MStefan99/OpenGimbal/3D/Head/Handle spacer.STEP

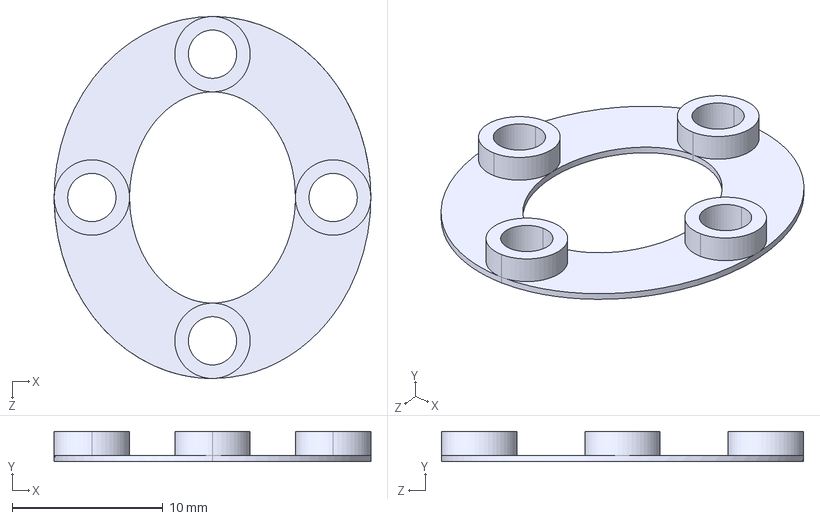
[picture p15: CAD file, 2026-09-18]
3D/Head/Handle spacer.STEP
21.0 x 2.00 x 24.0 mm
