MStefan99/OpenGimbal/3D/Head/Motor cover.STEP

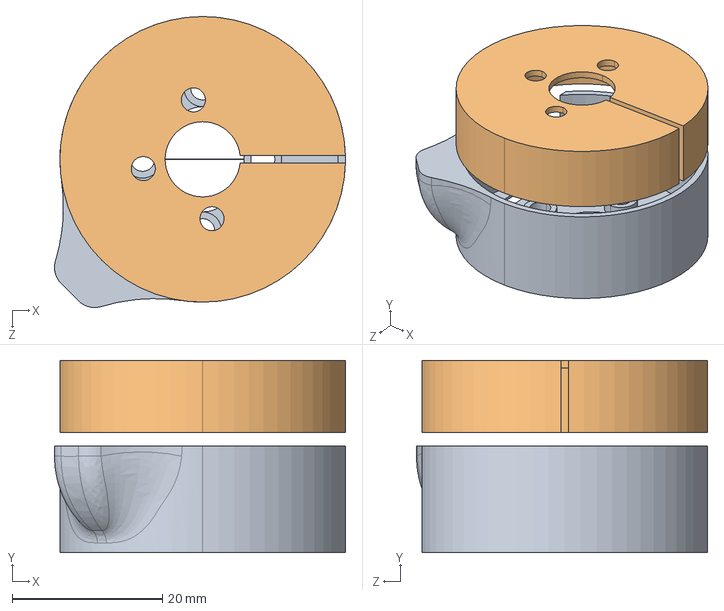
[picture p16: CAD file, 2026-09-18]
3D/Head/Motor cover.STEP
38.7 x 25.6 x 38.7 mm
