MStefan99/OpenGimbal/3D/Head/Upper arm.STEP

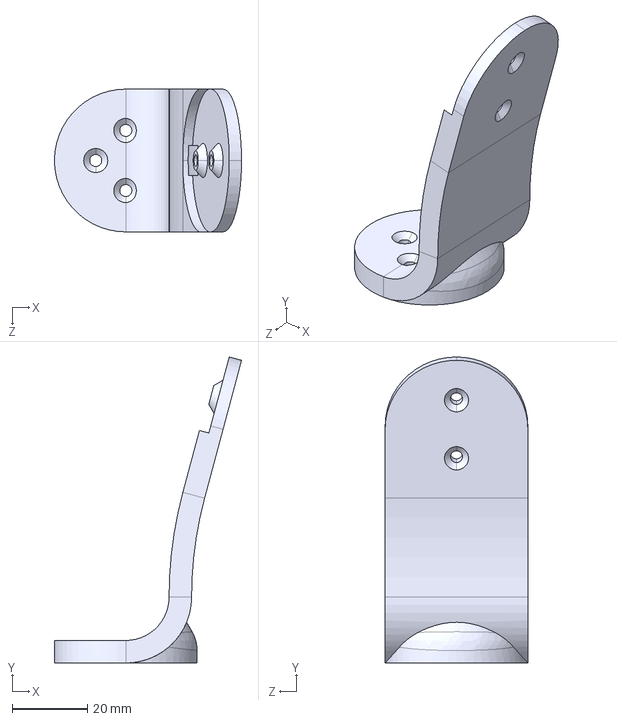
[picture p17: CAD file, 2026-09-18]
3D/Head/Upper arm.STEP
49.8 x 81.5 x 38.0 mm
