MStefan99/OpenGimbal/3D/Head/Motor cover upper.STEP

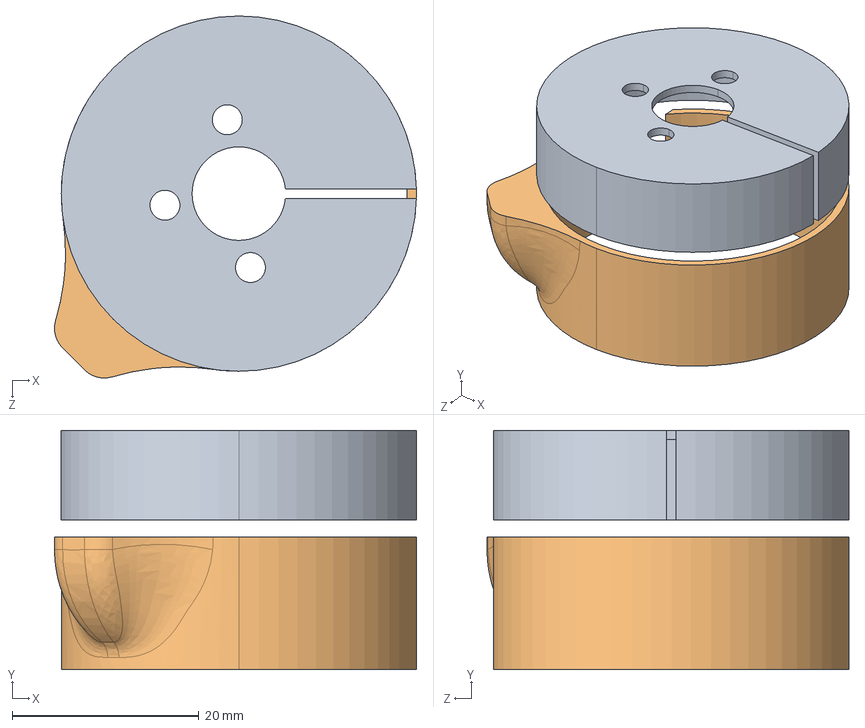
[picture p18: CAD file, 2026-09-18]
3D/Head/Motor cover upper.STEP
38.7 x 25.6 x 38.7 mm
