MStefan99/OpenGimbal/firmware/controller/src/usb.cpp

#include "usb.hpp"

using namespace usb;


static void controlHandler();
static void standardRequestHandler();
static void vendorRequestHandler();
static void enableEndpoints(uint8_t configurationNumber);
static void endpoint1Handler();


#define MIN(a, b) ((a < b) ? (a) : (b))


#define BMREQUESTTYPE_DPTD(bmRequestType)      ((bmRequestType & 0x80) >> 7)
#define BMREQUESTTYPE_TYPE(bmRequestType)      ((bmRequestType & 0x60) >> 5)
#define BMREQUESTTYPE_RECIPIENT(bmRequestType) (bmRequestType & 0x1f)

#define WVALUE_TYPE(wValue) ((wValue & 0xff00) >> 8)
#define WVALUE_IDX(wValue)  (wValue & 0xff)
#define WVALUE_ADD(wValue)  (wValue & 0x7f)

typedef struct __attribute__((packed)) {
	uint8_t  bmRequestType;
	uint8_t  bRequest;
	uint16_t wValue;
	uint16_t wIndex;
	uint16_t wLength;
} usb_device_endpoint0_request;

usb_descriptor_device_registers_t usb::EPDESCTBL[2];

static usb_device_endpoint0_request EP0REQ;
static usb_device_endpoint1_request EP1REQ;

static uint8_t* defaultData {nullptr};
static uint8_t  defaultLen {0};

static uint8_t outBuffer[128];

static usb::suspend_callback_type suspendCallback {nullptr};
static usb::callback_type         callback {nullptr};


extern "C" {
	void USB_Handler() {
		if (USB_REGS->DEVICE.USB_INTFLAG & USB_DEVICE_INTFLAG_SUSPEND_Msk) {  // Process USB reset
			USB_REGS->DEVICE.USB_INTFLAG = USB_DEVICE_INTFLAG_SUSPEND(1);       // Clear pending interrupt
			if (suspendCallback) {
				suspendCallback(true);
			}
		}

		if (USB_REGS->DEVICE.USB_INTFLAG & USB_DEVICE_INTFLAG_WAKEUP_Msk) {  // Process USB wakeup
			USB_REGS->DEVICE.USB_INTFLAG = USB_DEVICE_INTFLAG_WAKEUP(1);       // Clear pending interrupt
			if (suspendCallback) {
				suspendCallback(false);
			}
		}

		if (USB_REGS->DEVICE.USB_INTFLAG & USB_DEVICE_INTFLAG_EORST_Msk) {  // Process USB reset
			USB_REGS->DEVICE.USB_INTFLAG = USB_DEVICE_INTFLAG_EORST(1);       // Clear pending interrupt
			USB_REGS->DEVICE.DEVICE_ENDPOINT[0].USB_EPINTENSET =
			    USB_DEVICE_EPINTENSET_RXSTP(1)      // Enable SETUP endpoint interrupt
			    | USB_DEVICE_EPINTENSET_TRCPT0(1)   // Enable OUT endpoint interrupt
			    | USB_DEVICE_EPINTENSET_TRCPT1(1);  // Enable IN endpoint interrupt
			EPDESCTBL[0].DEVICE_DESC_BANK[0].USB_ADDR = (uint32_t)&EP0REQ;
		}

		if (USB_REGS->DEVICE.DEVICE_ENDPOINT[0].USB_EPINTFLAG
		    & (USB_DEVICE_EPINTFLAG_RXSTP_Msk | USB_DEVICE_EPINTFLAG_TRCPT1_Msk | USB_DEVICE_EPINTFLAG_TRCPT0_Msk)) {
			controlHandler();
		} else if (USB_REGS->DEVICE.DEVICE_ENDPOINT[1].USB_EPINTFLAG
		           & (USB_DEVICE_EPINTFLAG_TRCPT1_Msk | USB_DEVICE_EPINTFLAG_TRCPT0_Msk)) {
			endpoint1Handler();
			USB_REGS->DEVICE.DEVICE_ENDPOINT[1].USB_EPSTATUSCLR = USB_DEVICE_EPSTATUS_BK0RDY(1);
			USB_REGS->DEVICE.DEVICE_ENDPOINT[1].USB_EPINTFLAG =
			    USB_DEVICE_EPINTFLAG_Msk;  // Clear all pending endpoint interrupts
		}
	}
}

static void controlHandler() {
	if (USB_REGS->DEVICE.DEVICE_ENDPOINT[0].USB_EPINTFLAG & USB_DEVICE_EPINTFLAG_RXSTP_Msk) {  // Process SETUP transfers
		USB_REGS->DEVICE.DEVICE_ENDPOINT[0].USB_EPINTFLAG = USB_DEVICE_EPINTFLAG_RXSTP(1);       // Clear pending interrupt
		switch (static_cast<REQ_TYPE>(BMREQUESTTYPE_TYPE(EP0REQ.bmRequestType))) {
			case REQ_TYPE::STANDARD:
				standardRequestHandler();
				break;
			case REQ_TYPE::CLASS:
				// TODO: Handle
				break;
			case REQ_TYPE::VENDOR:
				vendorRequestHandler();
				break;
		}
		USB_REGS->DEVICE.DEVICE_ENDPOINT[0].USB_EPSTATUSSET = USB_DEVICE_EPSTATUS_BK1RDY(1);
		USB_REGS->DEVICE.DEVICE_ENDPOINT[0].USB_EPSTATUSCLR = USB_DEVICE_EPSTATUS_BK0RDY(1);
	}

	if (USB_REGS->DEVICE.DEVICE_ENDPOINT[0].USB_EPINTFLAG & USB_DEVICE_EPINTFLAG_TRCPT0_Msk) {  // Process OUT transfers
		USB_REGS->DEVICE.DEVICE_ENDPOINT[0].USB_EPINTFLAG = USB_DEVICE_EPINTFLAG_TRCPT0(1);       // Clear pending interrupt
		USB_REGS->DEVICE.DEVICE_ENDPOINT[0].USB_EPSTATUSSET = USB_DEVICE_EPSTATUS_BK1RDY(1);
	}

	if (USB_REGS->DEVICE.DEVICE_ENDPOINT[0].USB_EPINTFLAG & USB_DEVICE_EPINTFLAG_TRCPT1_Msk) {  // Process IN transfers
		USB_REGS->DEVICE.DEVICE_ENDPOINT[0].USB_EPINTFLAG = USB_DEVICE_EPINTFLAG_TRCPT1(1);       // Clear pending interrupt
		if (USB_REGS->DEVICE.USB_DADD && !(USB_REGS->DEVICE.USB_DADD & USB_DEVICE_DADD_ADDEN_Msk)) {
			USB_REGS->DEVICE.USB_DADD |= USB_DEVICE_DADD_ADDEN(1);
		}
	}
}

static void standardRequestHandler() {
	switch (static_cast<DEVICE_REQ>(EP0REQ.bRequest)) {
		case DEVICE_REQ::GET_DESCRIPTOR:
			switch (static_cast<DESCRIPTOR_TYPE>(WVALUE_TYPE(EP0REQ.wValue))) {
				case DESCRIPTOR_TYPE::DEVICE:
					EPDESCTBL[0].DEVICE_DESC_BANK[1].USB_ADDR = reinterpret_cast<uint32_t>(&DESCRIPTOR_DEVICE);
					EPDESCTBL[0].DEVICE_DESC_BANK[1].USB_PCKSIZE =
					    USB_DEVICE_PCKSIZE_BYTE_COUNT(MIN(DESCRIPTOR_DEVICE.bLength, EP0REQ.wLength))
					    | USB_DEVICE_PCKSIZE_SIZE(0x3) | USB_DEVICE_PCKSIZE_AUTO_ZLP(1);
					break;
				case DESCRIPTOR_TYPE::BOS:
					EPDESCTBL[0].DEVICE_DESC_BANK[1].USB_ADDR = reinterpret_cast<uint32_t>(&DESCRIPTOR_BOS);
					EPDESCTBL[0].DEVICE_DESC_BANK[1].USB_PCKSIZE =
					    USB_DEVICE_PCKSIZE_BYTE_COUNT(MIN(DESCRIPTOR_BOS.wTotalLength, EP0REQ.wLength))
					    | USB_DEVICE_PCKSIZE_SIZE(0x3) | USB_DEVICE_PCKSIZE_AUTO_ZLP(1);
					break;
				case DESCRIPTOR_TYPE::CONFIGURATION:
					EPDESCTBL[0].DEVICE_DESC_BANK[1].USB_ADDR =
					    reinterpret_cast<uint32_t>(&(DESCRIPTOR_CONFIGURATION[WVALUE_IDX(EP0REQ.wValue)]));
					EPDESCTBL[0].DEVICE_DESC_BANK[1].USB_PCKSIZE =
					    USB_DEVICE_PCKSIZE_BYTE_COUNT(
					        MIN(DESCRIPTOR_CONFIGURATION[WVALUE_IDX(EP0REQ.wValue)].wTotalLength, EP0REQ.wLength)
					    )
					    | USB_DEVICE_PCKSIZE_SIZE(0x3) | USB_DEVICE_PCKSIZE_AUTO_ZLP(1);
					break;
				case DESCRIPTOR_TYPE::STRING: {
					uint8_t idx = WVALUE_IDX(EP0REQ.wValue);
					if (idx <= sizeof(usb::DESCRIPTOR_STRING) / sizeof(usb::DESCRIPTOR_STRING[0])) {
						EPDESCTBL[0].DEVICE_DESC_BANK[1].USB_ADDR = reinterpret_cast<uint32_t>(&(DESCRIPTOR_STRING[idx]));
						EPDESCTBL[0].DEVICE_DESC_BANK[1].USB_PCKSIZE =
						    USB_DEVICE_PCKSIZE_BYTE_COUNT(MIN(DESCRIPTOR_STRING[idx].bLength, EP0REQ.wLength))
						    | USB_DEVICE_PCKSIZE_SIZE(0x3) | USB_DEVICE_PCKSIZE_AUTO_ZLP(1);
					} else {
						USB_REGS->DEVICE.DEVICE_ENDPOINT[0].USB_EPSTATUSSET = USB_DEVICE_EPSTATUSCLR_STALLRQ1(1);
					}
					break;
				}
				case DESCRIPTOR_TYPE::DEVICE_QUALIFIER:
					USB_REGS->DEVICE.DEVICE_ENDPOINT[0].USB_EPSTATUSSET = USB_DEVICE_EPSTATUSCLR_STALLRQ1(1);
					break;
				default:
					// TODO: Handle
					break;
			}
			USB_REGS->DEVICE.DEVICE_ENDPOINT[0].USB_EPSTATUSSET = USB_DEVICE_EPSTATUS_BK1RDY(1);
			break;
		case DEVICE_REQ::SET_ADDRESS:
			USB_REGS->DEVICE.USB_DADD = WVALUE_ADD(EP0REQ.wValue);
			EPDESCTBL[0].DEVICE_DESC_BANK[1].USB_PCKSIZE = USB_DEVICE_PCKSIZE_AUTO_ZLP(1);
			break;
		case DEVICE_REQ::SET_CONFIGURATION:
			EPDESCTBL[0].DEVICE_DESC_BANK[1].USB_PCKSIZE = USB_DEVICE_PCKSIZE_AUTO_ZLP(1);
			enableEndpoints(EP0REQ.wValue);
			break;
		default:
			// TODO: Handle
			break;
	}
}

static void vendorRequestHandler() {
	if (EP0REQ.bRequest == 0x01) {
		EPDESCTBL[0].DEVICE_DESC_BANK[1].USB_ADDR = reinterpret_cast<uint32_t>(&DESCRIPTOR_MS_OS_20);
		EPDESCTBL[0].DEVICE_DESC_BANK[1].USB_PCKSIZE =
		    USB_DEVICE_PCKSIZE_BYTE_COUNT(MIN(DESCRIPTOR_MS_OS_20.wTotalLength, EP0REQ.wLength))
		    | USB_DEVICE_PCKSIZE_SIZE(0x3) | USB_DEVICE_PCKSIZE_AUTO_ZLP(1);
	}
}

void endpoint1Handler() {
	if (USB_REGS->DEVICE.DEVICE_ENDPOINT[1].USB_EPINTFLAG & USB_DEVICE_EPINTFLAG_TRCPT0_Msk) {  // OUT transfer
		if (callback) {
			callback(EP1REQ, EPDESCTBL[1].DEVICE_DESC_BANK[0].USB_PCKSIZE & USB_DEVICE_PCKSIZE_BYTE_COUNT_Msk);
		}

		EPDESCTBL[1].DEVICE_DESC_BANK[0].USB_PCKSIZE =
		    USB_DEVICE_PCKSIZE_MULTI_PACKET_SIZE(sizeof(EP1REQ)) | USB_DEVICE_PCKSIZE_SIZE(0x3);
		return;
	} else if (defaultLen) {
		write(defaultData, defaultLen);
	}
}

static void enableEndpoints(uint8_t configurationNumber) {
	USB_REGS->DEVICE.DEVICE_ENDPOINT[1].USB_EPCFG =
	    USB_DEVICE_EPCFG_EPTYPE0(0x4)     // Configure endpoint 1 bank 0 as interrupt out
	    | USB_DEVICE_EPCFG_EPTYPE1(0x4);  // Configure endpoint 1 bank 1 as interrupt in
	EPDESCTBL[1].DEVICE_DESC_BANK[0].USB_ADDR = reinterpret_cast<uint32_t>(&EP1REQ);
	EPDESCTBL[1].DEVICE_DESC_BANK[0].USB_PCKSIZE =
	    USB_DEVICE_PCKSIZE_MULTI_PACKET_SIZE(sizeof(EP1REQ)) | USB_DEVICE_PCKSIZE_SIZE(0x3);
	USB_REGS->DEVICE.DEVICE_ENDPOINT[1].USB_EPINTENSET = USB_DEVICE_EPINTENSET_TRCPT0(1)  // Enable OUT endpoint interrupt
	                                                   | USB_DEVICE_EPINTENSET_TRCPT1(1);  // Enable IN endpoint interrupt
}

void usb::init() {
	auto id = (reinterpret_cast<uint32_t*>(0x0080A00C));

	usb::DESCRIPTOR_STRING[3].bLength = 66;
	for (uint8_t i {0}; i < 4; ++i) {
		uint32_t word {id[i]};
		for (int8_t j {7}; j >= 0; --j) {
			uint8_t c = word & 0xf;
			usb::DESCRIPTOR_STRING[3].bString[8 * i + j] = c + (c < 0xa ? 0x0030 : 0x0037);
			word = word >> 4u;
		}
	}

	GCLK_REGS->GCLK_PCHCTRL[USB_GCLK_ID] = GCLK_PCHCTRL_CHEN(1)     // Enable USB clock
	                                     | GCLK_PCHCTRL_GEN_GCLK1;  // Set GCLK1 as a clock source

	NVIC_EnableIRQ(USB_IRQn);

	PORT_REGS->GROUP[0].PORT_PINCFG[24] = PORT_PINCFG_PMUXEN(1);  // Enable mux on pin 24
	PORT_REGS->GROUP[0].PORT_PINCFG[25] = PORT_PINCFG_PMUXEN(1);  // Enable mux on pin 25
	PORT_REGS->GROUP[0].PORT_PMUX[12] = PORT_PMUX_PMUXE_G         // Mux pin 24 to USB
	                                  | PORT_PMUX_PMUXO_G;        // Mux pin 25 to USB

	USB_REGS->DEVICE.USB_PADCAL =
	    USB_PADCAL_TRANSN(
	        (OTP5_FUSES_REGS->FUSES_OTP5_WORD_0 & FUSES_OTP5_WORD_0_USB_TRANSN_Msk) >> FUSES_OTP5_WORD_0_USB_TRANSN_Pos
	    )
	    | USB_PADCAL_TRANSP(
	        (OTP5_FUSES_REGS->FUSES_OTP5_WORD_0 & FUSES_OTP5_WORD_0_USB_TRANSP_Msk) >> FUSES_OTP5_WORD_0_USB_TRANSP_Pos
	    )
	    | USB_PADCAL_TRIM(
	        (OTP5_FUSES_REGS->FUSES_OTP5_WORD_0 & FUSES_OTP5_WORD_0_USB_TRIM_Msk) >> FUSES_OTP5_WORD_0_USB_TRIM_Pos
	    );                                                                          // USB pad calibration
	USB_REGS->DEVICE.USB_CTRLA = USB_CTRLA_ENABLE(1)                                // Enable USB
	                           | USB_CTRLA_MODE_DEVICE;                             // Enable in device mode
	USB_REGS->DEVICE.DEVICE_ENDPOINT[0].USB_EPCFG = USB_DEVICE_EPCFG_EPTYPE0(0x1)   // Configure endpoint 0 as setup out
	                                              | USB_DEVICE_EPCFG_EPTYPE1(0x1);  // Configure endpoint 0 as setup in
	USB_REGS->DEVICE.USB_DESCADD = reinterpret_cast<uint32_t>(&EPDESCTBL);          // Setting endpoint descriptor address
	USB_REGS->DEVICE.USB_CTRLB = USB_DEVICE_CTRLB_DETACH(0);                        // Attach to host
	USB_REGS->DEVICE.USB_INTENSET = USB_DEVICE_INTENSET_EORST(1)                    // Enable end-of-reset interrupt
	                              | USB_DEVICE_INTENSET_WAKEUP(1)                   // Enable wakeup interrupt
	                              | USB_DEVICE_INTENSET_SUSPEND(1);                 // Enable suspend interrupt
}

bool usb::isActive() {
	return USB_REGS->DEVICE.USB_FSMSTATUS != USB_FSMSTATUS_FSMSTATE_OFF
	    && USB_REGS->DEVICE.USB_FSMSTATUS != USB_FSMSTATUS_FSMSTATE_SUSPEND;
}

void usb::writeDefault(uint8_t* data, uint8_t len) {
	defaultData = data;
	defaultLen = len;

	if (!(USB_REGS->DEVICE.DEVICE_ENDPOINT[1].USB_EPSTATUS & USB_DEVICE_EPSTATUS_BK1RDY(0))) {
		write(data, len);
	}
}

void usb::write(const uint8_t* data, uint8_t len) {
	util::copy(outBuffer, data, len);
	EPDESCTBL[1].DEVICE_DESC_BANK[1].USB_ADDR = reinterpret_cast<uint32_t>(outBuffer);
	EPDESCTBL[1].DEVICE_DESC_BANK[1].USB_PCKSIZE =
	    USB_DEVICE_PCKSIZE_BYTE_COUNT(len) | USB_DEVICE_PCKSIZE_SIZE(0x3) | USB_DEVICE_PCKSIZE_AUTO_ZLP(1);
	USB_REGS->DEVICE.DEVICE_ENDPOINT[1].USB_EPSTATUSSET = USB_DEVICE_EPSTATUS_BK1RDY(1);
}

void usb::setSuspendCallback(suspend_callback_type cb) {
	suspendCallback = cb;
}

void usb::setCallback(callback_type cb) {
	callback = cb;
}
