MStefan99/OpenGimbal/firmware/driver/main.hpp

/*
 * File:   main.hpp
 * Author: Mikhail
 *
 * Created on November 8, 2023, 5:24 PM
 */

#ifndef MAIN_HPP
#define MAIN_HPP

#include "device.h"
// #include <xc.h>  // TODO: explore, possibly delete Harmony files

// #include <cstdio>
// #include <cinttypes>

#include "AS5600.hpp"
#include "bldc.hpp"
#include "eic.hpp"
#include "i2c.hpp"
#include "Kalman.hpp"
#include "LowPassFilter.hpp"
#include "Matrix.hpp"
#include "MovementController.hpp"
#include "nvm.hpp"
#include "PID.hpp"
#include "Response.hpp"
#include "uart.hpp"
#include "util.hpp"


enum class Mode : uint8_t {
	Sleep = 0x0,
	Calibrate = 0x1,
	Drive = 0x2,
	Haptic = 0x3,
	Idle = 0x04
};

#endif /* MAIN_HPP */
