MStefan99/OpenGimbal/firmware/controller/src/adc.cpp

#include "adc.hpp"

struct queueEntry {
	adc::Callback cb {nullptr};
	uint16_t      input {};
};

static RingBuffer<queueEntry, uint8_t, 4> measureQueue {};


extern "C" {
	void ADC_Handler() {
		if (measureQueue.size()) {
			auto cb {measureQueue.front().cb};

			if (cb) {
				cb(ADC_REGS->ADC_RESULT);
			}
			measureQueue.pop_front();

			if (measureQueue.size()) {
				ADC_REGS->ADC_INPUTCTRL = ADC_INPUTCTRL_MUXNEG_GND     // Set GND as negative input
				                        | measureQueue.front().input;  // Set temperature sensor as positive input

				ADC_REGS->ADC_SWTRIG = ADC_SWTRIG_START(1);
			}
		}

		ADC_REGS->ADC_INTFLAG = ADC_INTFLAG_Msk;
	}
}

void adc::init() {
	// Clock setup
	GCLK_REGS->GCLK_PCHCTRL[ADC_GCLK_ID] = GCLK_PCHCTRL_CHEN(1)     // Enable ADC clock
	                                     | GCLK_PCHCTRL_GEN_GCLK2;  // Set GCLK2 as a clock source

	// Voltage reference setup
	SUPC_REGS->SUPC_VREF = SUPC_VREF_TSEN(1)      // Enable temperature sensor
	                     | SUPC_VREF_ONDEMAND(1)  // Only enable if requested
	                     | SUPC_VREF_SEL_1V0;     // Set 1.0V as a reference

	// Pin setup
	PORT_REGS->GROUP[0].PORT_WRCONFIG = PORT_WRCONFIG_PINMASK(0x1 << 2u | 0x1 << 3u | 0x1 << 6u)  // Select pins
	                                  | PORT_WRCONFIG_PMUXEN(1)                                   // Enable multiplexing
	                                  | PORT_WRCONFIG_PMUX(MUX_PA02B_ADC_AIN0)                    // Multiplex to ADC
	                                  | PORT_WRCONFIG_WRPMUX(1)     // Write pin multiplex settings
	                                  | PORT_WRCONFIG_WRPINCFG(1);  // Write pin config settings

	// ADC setup
	ADC_REGS->ADC_CTRLB = ADC_CTRLB_PRESCALER_DIV32;  // Set prescaler
	ADC_REGS->ADC_CALIB = ADC_CALIB_BIASREFBUF(
	                          (OTP5_FUSES_REGS->FUSES_OTP5_WORD_0 & FUSES_OTP5_WORD_0_ADC_BIASREFBUF_Msk)
	                          >> FUSES_OTP5_WORD_0_ADC_BIASREFBUF_Pos
	                      )
	                    | ADC_CALIB_BIASCOMP(
	                          (OTP5_FUSES_REGS->FUSES_OTP5_WORD_0 & FUSES_OTP5_WORD_0_ADC_BIASCOMP_Msk)
	                          >> FUSES_OTP5_WORD_0_ADC_BIASCOMP_Pos
	                    );
	ADC_REGS->ADC_SAMPCTRL = ADC_SAMPCTRL_OFFCOMP(1);                         // Enable offset compensation
	ADC_REGS->ADC_AVGCTRL = ADC_AVGCTRL_SAMPLENUM_8 | ADC_AVGCTRL_ADJRES(3);  // Enable averaging
	ADC_REGS->ADC_CTRLC = ADC_CTRLC_RESSEL_16BIT;
	ADC_REGS->ADC_INTENSET = ADC_INTENSET_RESRDY(1);     // Enable result ready interrupt
	ADC_REGS->ADC_REFCTRL = ADC_REFCTRL_REFSEL_INTVCC2;  // Set ADC reference voltage
	ADC_REGS->ADC_CTRLA =                                // ADC_CTRLA_RUNSTDBY(1)           // Enable in standby mode
	    ADC_CTRLA_ONDEMAND(1)                            // Only enable if requested
	    | ADC_CTRLA_ENABLE(1);                           // Enable ADC

	NVIC_EnableIRQ(ADC_IRQn);
}

static void measure(void (*cb)(uint16_t), uint16_t input) {
	measureQueue.push_back({cb, input});

	if (measureQueue.size() == 1) {
		ADC_REGS->ADC_INPUTCTRL = ADC_INPUTCTRL_MUXNEG_GND  // Set GND as negative input
		                        | input;                    // Set temperature sensor as positive input

		ADC_REGS->ADC_SWTRIG = ADC_SWTRIG_START(1);
	}
}

void adc::measureTemperature(void (*cb)(uint16_t)) {
	measure(cb, ADC_INPUTCTRL_MUXPOS_TEMP);  // Set temperature sensor as positive input
}

void adc::measureBattery(void (*cb)(uint16_t)) {
	measure(cb, ADC_INPUTCTRL_MUXPOS_AIN6);  // Set battery pin as positive input
}

void adc::measureX(void (*cb)(uint16_t)) {
	measure(cb, ADC_INPUTCTRL_MUXPOS_AIN0);  // Set X axis pin as positive input
}

void adc::measureY(void (*cb)(uint16_t)) {
	measure(cb, ADC_INPUTCTRL_MUXPOS_AIN1);  // Set Y axis pin as positive input
}
