MStefan99/OpenGimbal/firmware/controller/inc/HostResponse.hpp

/*
 * File:   USBCommand.hpp
 * Author: Mikhail
 *
 * Created on June 22, 2023, 17:58 PM
 */

#ifndef HOST_RESPONSE_HPP
#define HOST_RESPONSE_HPP

#include "device.h"

#include "util.hpp"

namespace HostCommand {
	enum class CommandType : uint8_t {
		Sleep = 0x0,
		Wake = 0x1,
		Discovery = 0x0c,
		SetVariable = 0x0d,
		GetVariable = 0x0e,
		MotorPassthrough = 0x0f
	};

	enum class Variable : uint8_t {
		Orientation = 0x00,
		HandleOrientation = 0x01,
		Mode = 0x02,
		BatteryVoltage = 0x03,
		DeviceVersion = 0x10,
		VendorName = 0x11,
		ProductName = 0x12,
		SerialNumber = 0x13
	};
}

class HostResponse {
public:
	using buffer_type = uint8_t[128];
	using size_type = uint8_t;

	using Variable = HostCommand::Variable;

	enum class ResponseType : uint8_t {
		Discovery = 0xd,
		ReturnVariable = 0xe,
		MotorPassthrough = 0xf
	};

	struct __attribute__((packed)) USBOrientationResponse {
		int16_t yaw;
		int16_t pitch;
		int16_t roll;
	};

	struct __attribute__((packed)) USBSensorResponse {
		int16_t accelerations[3];  // ZYX
		int16_t angularRates[3];   // Yaw - pitch - roll
	};

	HostResponse() = default;
	HostResponse(ResponseType type, uint8_t dataLength);

	buffer_type& getBuffer();
	size_type    getLength();

protected:
	buffer_type _buffer = {0};
	size_type   _length {0};
};

class HostReturnVariableResponse: public HostResponse {
public:
	template <class T>
	HostReturnVariableResponse(HostResponse::Variable variable, T value);
	HostReturnVariableResponse(HostResponse::Variable variable, const uint8_t* data = nullptr, uint8_t len = 0);
};

template <class T>
HostReturnVariableResponse::HostReturnVariableResponse(HostResponse::Variable variable, T value):
  HostResponse {ResponseType::ReturnVariable, 1 + sizeof(T)} {
	this->_buffer[1] = static_cast<uint8_t>(variable);

	for (size_type i {0}; i < sizeof(T); ++i) {
		this->_buffer[sizeof(T) + 1 - i] = value;
		value >>= 8;
	}
}


#endif /* DATA_HPP */
