MStefan99/OpenGimbal/firmware/controller/src/joystick.cpp

#include "joystick.hpp"

constexpr int deadzone = joystick::deadzone * joystick::deadzone;

static uint16_t        values[2] {};
static nvm::AxisPoints axisPoints[2] {};

volatile static joystick::callback_type callback {nullptr};
volatile static uint32_t                lastUpdateTime {0};

void joystick::update(callback_type cb) {
	if (util::getTime() - lastUpdateTime > 20) {
		callback = nullptr;
	}
	if (callback) {
		return;
	}

	callback = cb;
	lastUpdateTime = util::getTime();

	adc::measureX([](uint16_t x) {
		values[0] = x;

		adc::measureY([](uint16_t y) {
			values[1] = y;

			for (uint8_t i {0}; i < 2; ++i) {
				if (values[i] < axisPoints[i].min) {
					axisPoints[i].min = values[i];
				}
				if (values[i] > axisPoints[i].max) {
					axisPoints[i].max = values[i];
				}
			}

			callback(getAxis(0), getAxis(1));
			callback = nullptr;
		});
	});
}

int16_t joystick::getAxis(uint8_t axis) {
	axis %= 2;

	int16_t dx = values[0] - axisPoints[0].center;
	int16_t dy = values[1] - axisPoints[1].center;

	if (dx * dx + dy * dy < deadzone) {
		return 0;
	} else if (values[axis] < axisPoints[axis].center - joystick::deadzone) {
		return util::scale<int16_t>(
		    values[axis],
		    axisPoints[axis].min,
		    axisPoints[axis].center - joystick::deadzone,
		    -1000,
		    0
		);
	} else if (values[axis] > axisPoints[axis].center + joystick::deadzone) {
		return util::scale<int16_t>(
		    values[axis],
		    axisPoints[axis].center + joystick::deadzone,
		    axisPoints[axis].max,
		    0,
		    1000
		);
	}
	return 0;
}

void joystick::updateCenter() {
	update([](int16_t x, int16_t y) {  // x and y are not used here
		for (uint8_t i {0}; i < 2; ++i) {
			if (!axisPoints[i].center) {
				axisPoints[i].center = values[i];
			} else {
				axisPoints[i].center = (axisPoints[i].center + values[i]) / 2;
			}
		}
	});
}

void joystick::saveValues() {
	nvm::edit(&nvm::options.xAxisPoints, axisPoints[0]);
	nvm::edit(&nvm::options.yAxisPoints, axisPoints[1]);
	nvm::write();
}
