MStefan99/OpenGimbal/firmware/driver/inc/bldc.h

/* 
 * File:   interop.h
 * Author: Mikhail
 *
 * Created on April 9, 2024, 5:59 PM
 */

#ifndef INTEROP_H
#define	INTEROP_H


#ifdef	__cplusplus
extern "C" {
#endif

    void bldcDisable();

#ifdef	__cplusplus
}
#endif

#endif	/* INTEROP_H */
