MStefan99/OpenGimbal/firmware/driver/src/util.cpp

#include "util.hpp"


static uint32_t ticks {0};

extern "C" {
	void SysTick_Handler() {
		++ticks;
	}
}

void util::init() {
	uint32_t calibration = *((uint32_t*)0x00806020);

	// Supply setup
	SUPC_REGS->SUPC_VREG = SUPC_VREG_ENABLE(1);  // Enable regulator
	while (!(SUPC_REGS->SUPC_STATUS & SUPC_INTFLAG_VREGRDY_Msk));

	// Performance setup
	NVMCTRL_REGS->NVMCTRL_CTRLB = NVMCTRL_CTRLB_MANW(1)     // Use NVM in manual write mode
	                            | NVMCTRL_CTRLB_RWS(2);     // Use 2 wait states for NVM
	PM_REGS->PM_PLCFG = PM_PLCFG_PLSEL_PL2;                 // Enter PL2
	while (!(PM_REGS->PM_INTFLAG & PM_INTFLAG_PLRDY_Msk));  // Wait for the transition to complete

	// Clock setup
	// Enable DFLL
	OSCCTRL_REGS->OSCCTRL_DFLLVAL = OSCCTRL_DFLLVAL_COARSE(calibration >> 26u)  // Load calibration value
	                              | OSCCTRL_DFLLVAL_FINE(512);  // Middle value for FINE (0-1023) is a good starting point
	OSCCTRL_REGS->OSCCTRL_DFLLCTRL = OSCCTRL_DFLLCTRL_ENABLE(1)    // Enable DFLL48M
	                               | OSCCTRL_DFLLCTRL_ONDEMAND(1)  // Only run when requested
	                               | OSCCTRL_DFLLCTRL_MODE(0);     // Run in open-loop mode

	// Switch the CPU over to DFLL
	GCLK_REGS->GCLK_GENCTRL[0] = GCLK_GENCTRL_GENEN(1)                                     // Enable GCLK 0
	                           | OSCCTRL_DFLLCTRL_ONDEMAND(1) | GCLK_GENCTRL_SRC_DFLL48M;  // Set DFLL48M as a source

	while (!(OSCCTRL_REGS->OSCCTRL_STATUS & OSCCTRL_STATUS_DFLLRDY_Msk));  // Wait for DFLL to start

	// Enable OSC16M
	OSCCTRL_REGS->OSCCTRL_OSC16MCTRL = OSCCTRL_OSC16MCTRL_ENABLE(1)    // Enable OSC16M
	                                 | OSCCTRL_OSC16MCTRL_ONDEMAND(1)  // Only run when requested
	                                 | OSCCTRL_OSC16MCTRL_FSEL_16;     // Set frequency to 16MHz

	// Enable generic clocks
	GCLK_REGS->GCLK_GENCTRL[1] = GCLK_GENCTRL_GENEN(1)      // Enable GCLK 1
	                           | GCLK_GENCTRL_SRC_DFLL48M;  // Set DFLL48M as a source
	GCLK_REGS->GCLK_GENCTRL[2] = GCLK_GENCTRL_GENEN(1)      // Enable GCLK 2
	                           | GCLK_GENCTRL_SRC_OSC16M;   // Set OSC16M as a source

	// RTC setup
	OSC32KCTRL_REGS->OSC32KCTRL_RTCCTRL = OSC32KCTRL_RTCCTRL_RTCSEL_ULP32K;

	RTC_REGS->MODE0.RTC_CTRLA = RTC_MODE0_CTRLA_ENABLE(1)      // Enable RTC
	                          | RTC_MODE0_CTRLA_MODE_COUNT32   // Count in 32-bit mode
	                          | RTC_MODE0_CTRLA_MATCHCLR(0)    // Do not clear on match
	                          | RTC_MODE0_CTRLA_COUNTSYNC(1);  // Enable count register sync

	// SysTick setup
	SysTick_Config(48000);

	// NVIC setup
	__DMB();
	__enable_irq();
	NVIC_EnableIRQ(SysTick_IRQn);
}

uint32_t util::getTime() {
	return ticks;
}

void util::sleep(uint32_t ms) {
	uint32_t start {ticks};

	while (ticks - start < ms) {
		__WFI();
	}
}
